lm-hotton/ProjetCapteurGraphite2022-LM-TL/APK_CapteurGraphite/Graph.png

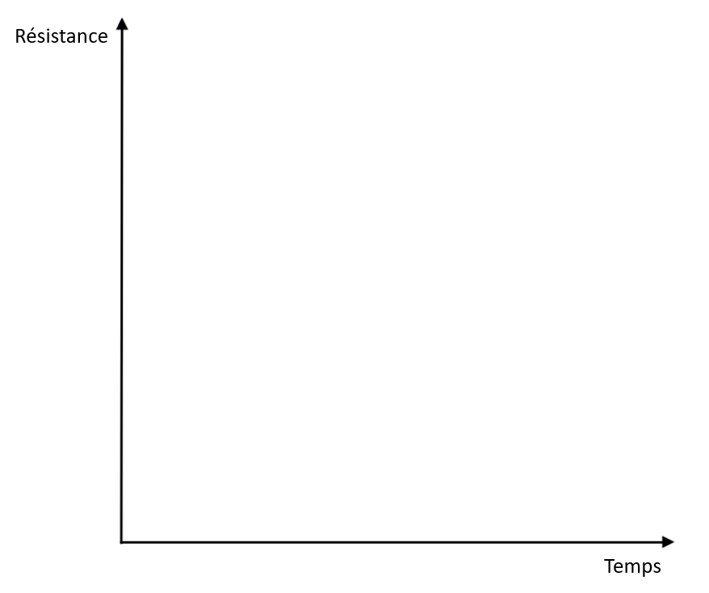
APK_CapteurGraphite/Graph.png
