lm-hotton/ProjetCapteurGraphite2022-LM-TL/Photos_LTSpice/50Hz.png

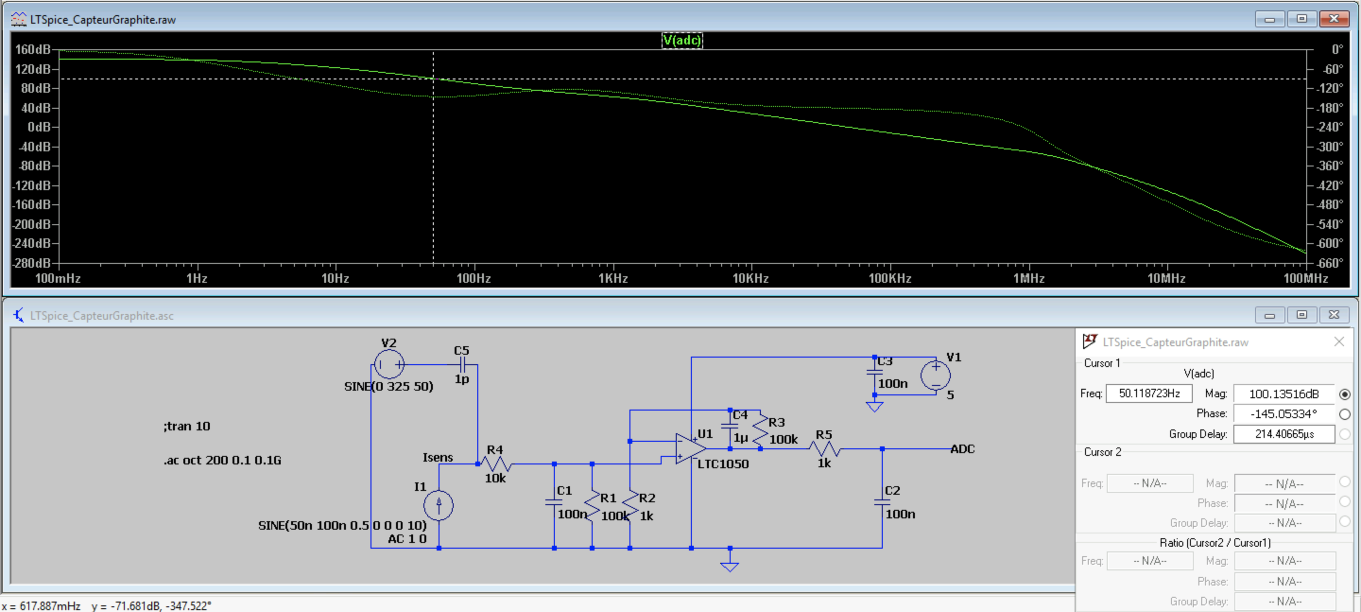
Photos_LTSpice/50Hz.png
