lm-hotton/ProjetCapteurGraphite2022-LM-TL/Photos_LTSpice/FiltreTotal.png

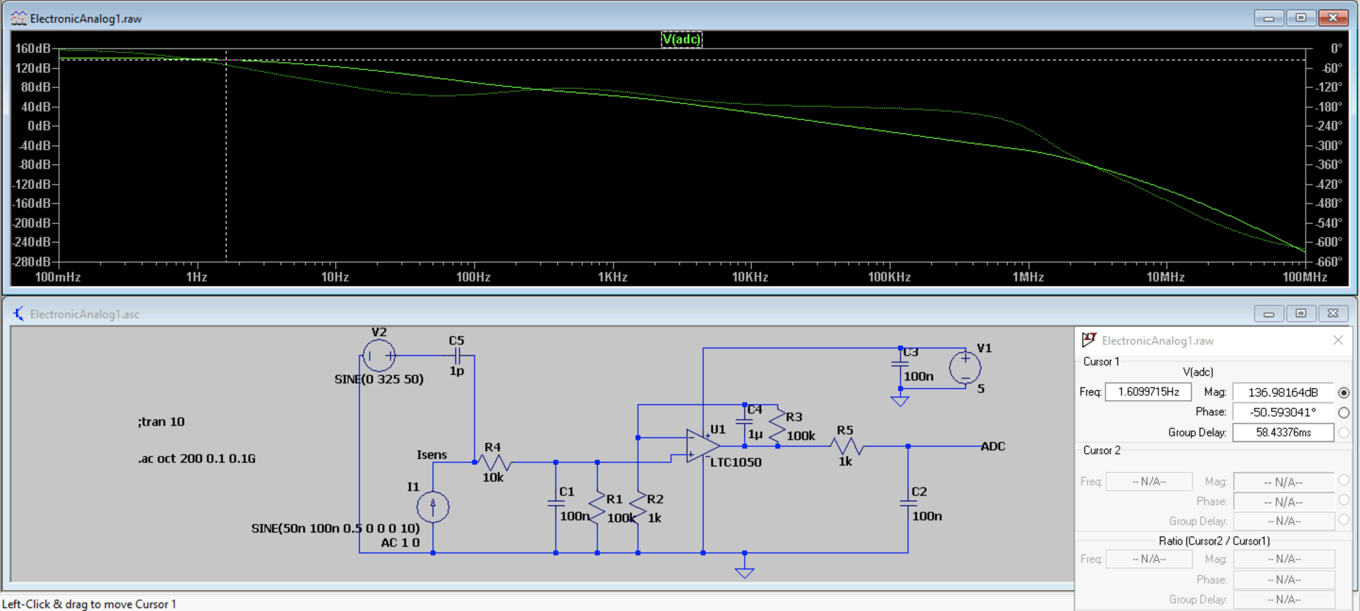
Photos_LTSpice/FiltreTotal.png
