lm-hotton/ProjetCapteurGraphite2022-LM-TL/Photos_LTSpice/PhotoLTSpice11.png

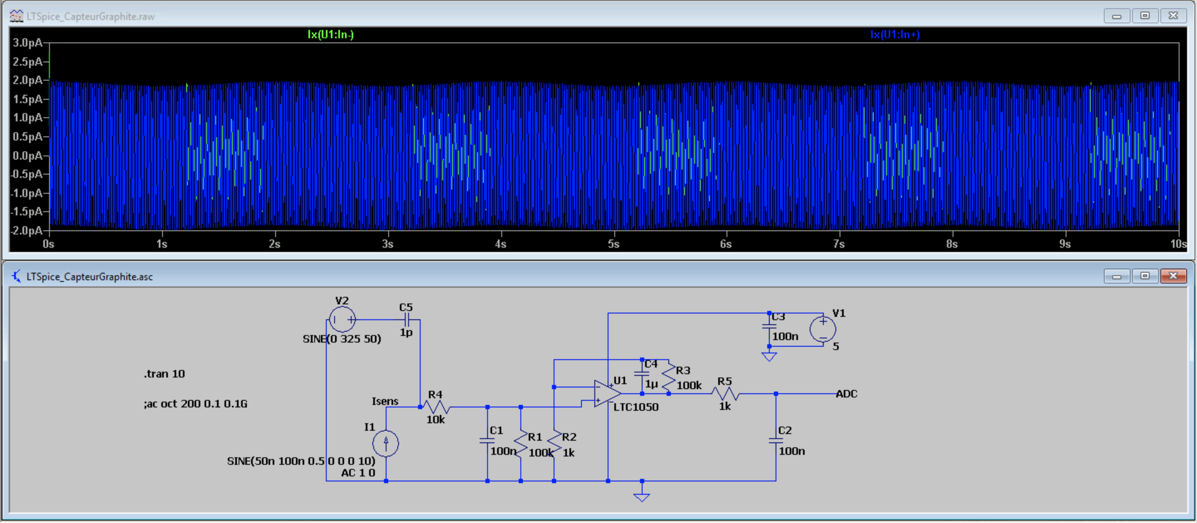
Photos_LTSpice/PhotoLTSpice11.png
