lm-hotton/ProjetCapteurGraphite2022-LM-TL/Photos_LTSpice/PhotoLTSpice13.png

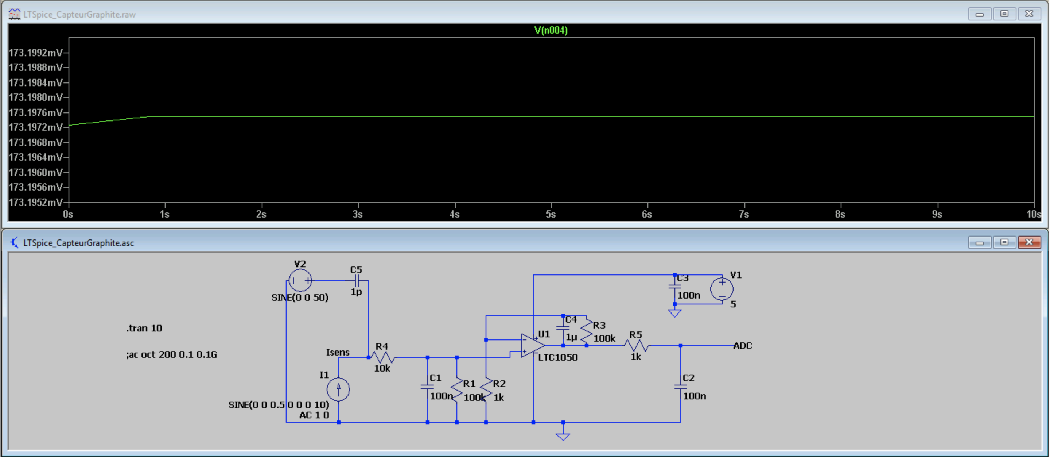
Photos_LTSpice/PhotoLTSpice13.png
