lm-hotton/ProjetCapteurGraphite2022-LM-TL/LTSpice/SchemaCompletAvecCapteur/ElectronicAnalog1.asc

C1: cap; 100n
C2: cap; 100n
C3: cap; 1p
C4: cap; 1µ
C5: cap; 100n
R1: res; 100k
R2: res; 1k
R3: res; 100k
R4: res; 10k
R5: res; 1k
U1: LTC1050
V1: voltage; SINE(5 0 05 50)
V2: voltage; SINE(0 325 50)
V3: voltage; PULSE(0 1 0.2 0.1 00.1 20); AC 1
X2: GP_Capteur
Named nets: 0, ADC, Vemp, Vep
.tran 10
;ac oct 200 0.1 0.1G
