lm-hotton/ProjetCapteurGraphite2022-LM-TL/LTSpice/TestPasseBas/TestPasseBas.asc

C1: cap; 100p
R1: res; 10k
V1: voltage; PULSE(0 1 10u 0.1u 0.1u 10u); AC 1 0
Named nets: Vout, 0
;tran 30u
.ac dec 100 1 1G
