lm-hotton/ProjetCapteurGraphite2022-LM-TL/LTSpice/Draft/Draft1.asc

C1: cap; 200µ
R1: res; 1k
Named nets: gp, gn, gc
