lm-hotton/ProjetCapteurGraphite2022-LM-TL/LTSpice/GP_Capteur/GP_Capteur.asc

B1: bi; I=V(cp,cn)*(10n+v(gc,gn)*10n)
C1: cap; 200µ
R1: res; 1k
Named nets: gp, gn, gc, cp, cn
